heniekstar/DenshaDeGo_controller/pics/MAIN_BOARD_N64.JPG

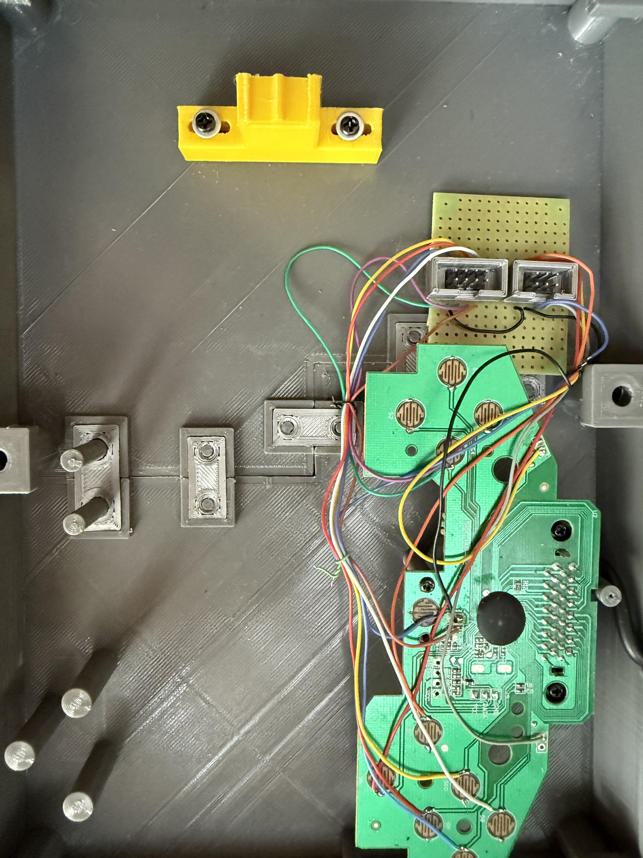
pics/MAIN_BOARD_N64.JPG
