heniekstar/DenshaDeGo_controller/pics/POGO_2.JPG

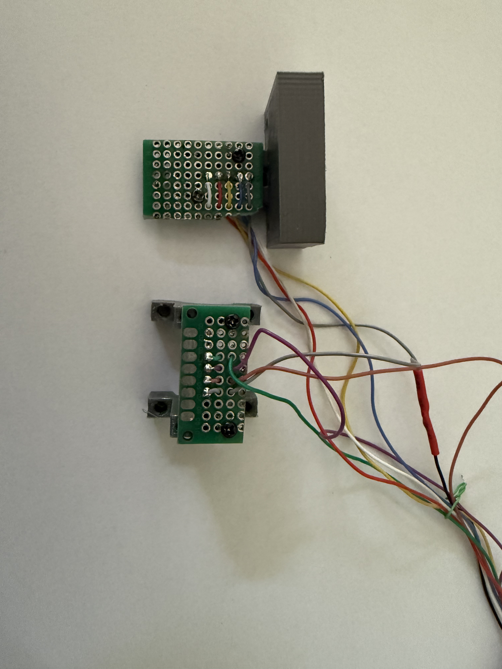
pics/POGO_2.JPG
