heniekstar/DenshaDeGo_controller/pics/POGO_POWER_WHEELS_2.JPG

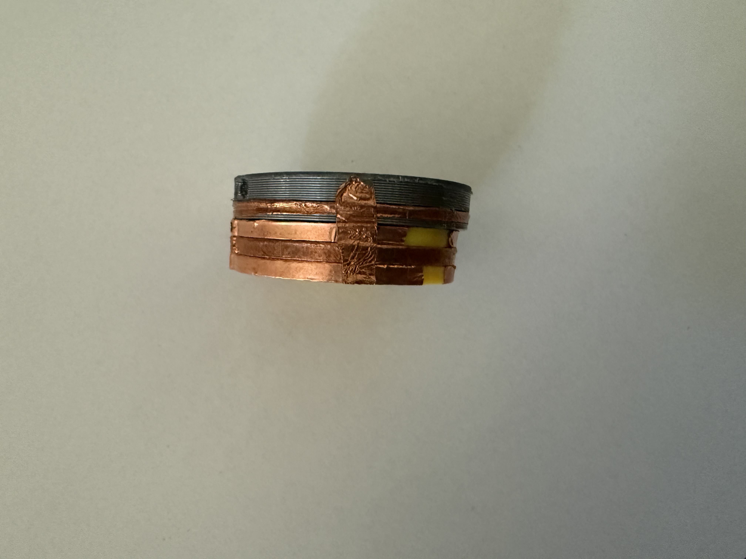
pics/POGO_POWER_WHEELS_2.JPG
