heniekstar/DenshaDeGo_controller/Limit_switch/DDG_BRAKE_WHEEL_3.stl

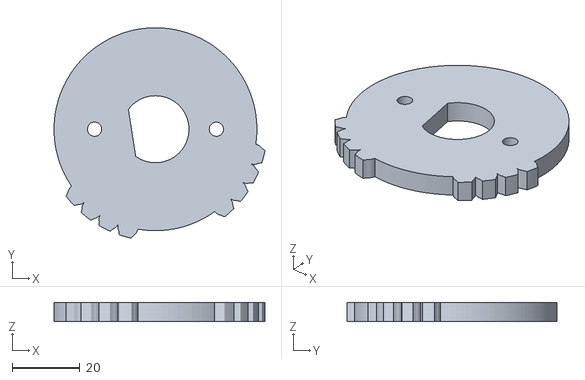
[picture p24: CAD file, 2026-08-02]
Limit_switch/DDG_BRAKE_WHEEL_3.stl
62.4 x 62.2 x 5.70
