heniekstar/DenshaDeGo_controller/Pogo/DDG_POGO_BREAK_WHEEL_2.stl

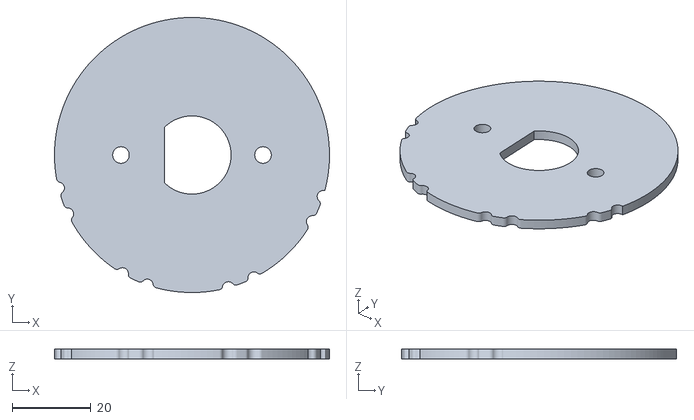
[picture p25: CAD file, 2026-08-02]
Pogo/DDG_POGO_BREAK_WHEEL_2.stl
69.7 x 69.7 x 2.50
