heniekstar/DenshaDeGo_controller/Limit_switch/DDG_BRAKE_WHEEL_4.stl

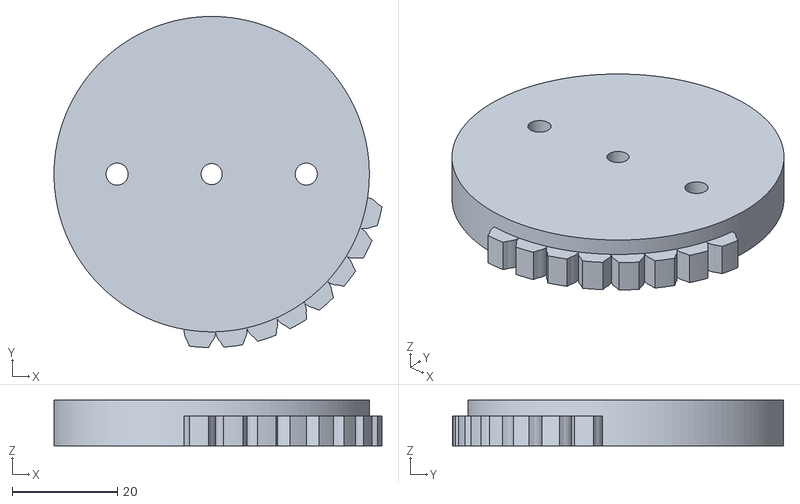
[picture p26: CAD file, 2026-08-02]
Limit_switch/DDG_BRAKE_WHEEL_4.stl
62.4 x 63.0 x 8.70
