heniekstar/DenshaDeGo_controller/Pogo/DDG_POGO_BREAK_WHEEL_0.stl

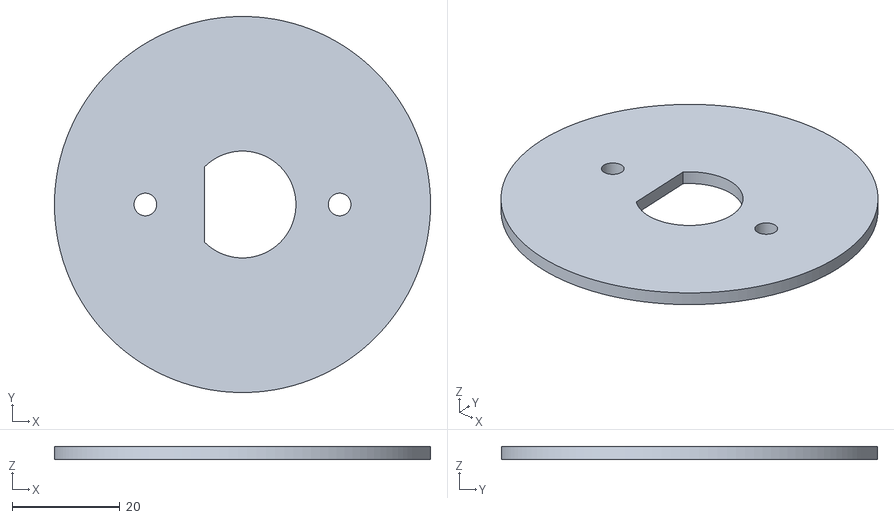
[picture p27: CAD file, 2026-08-02]
Pogo/DDG_POGO_BREAK_WHEEL_0.stl
69.7 x 69.7 x 2.50
