heniekstar/DenshaDeGo_controller/Pogo/DDG_POGO_POWER_WHEEL_MAG.stl

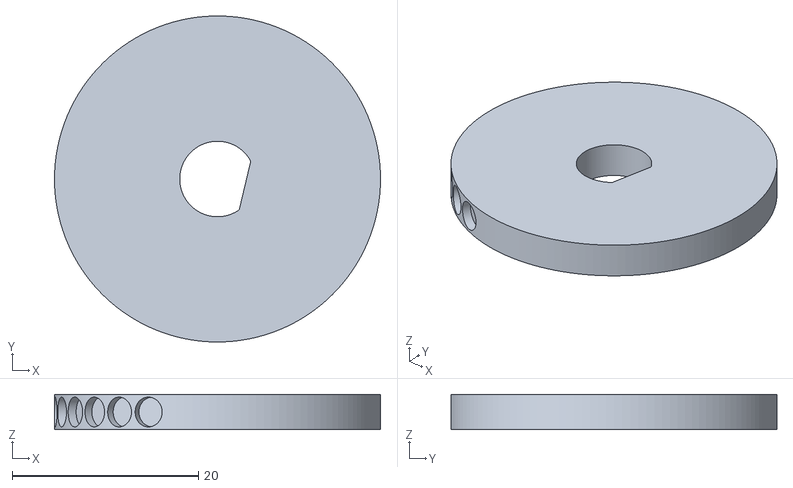
[picture p28: CAD file, 2026-08-02]
Pogo/DDG_POGO_POWER_WHEEL_MAG.stl
35.0 x 35.0 x 3.80
