heniekstar/DenshaDeGo_controller/Pogo/DDG_POGO_BREAK_WHEEL_SUPPORT.stl

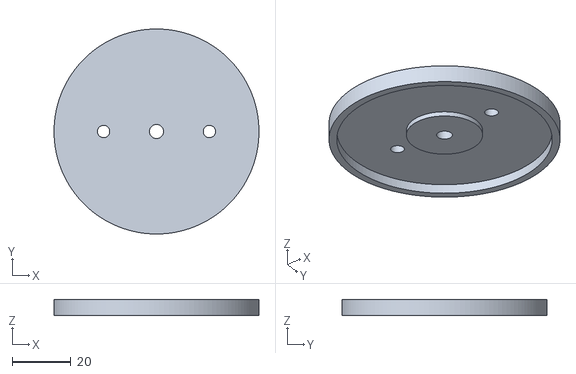
[picture p29: CAD file, 2026-08-02]
Pogo/DDG_POGO_BREAK_WHEEL_SUPPORT.stl
69.7 x 69.7 x 5.50
