heniekstar/DenshaDeGo_controller/Pogo/DDG_POWER_HANDLE_END_CAP.stl

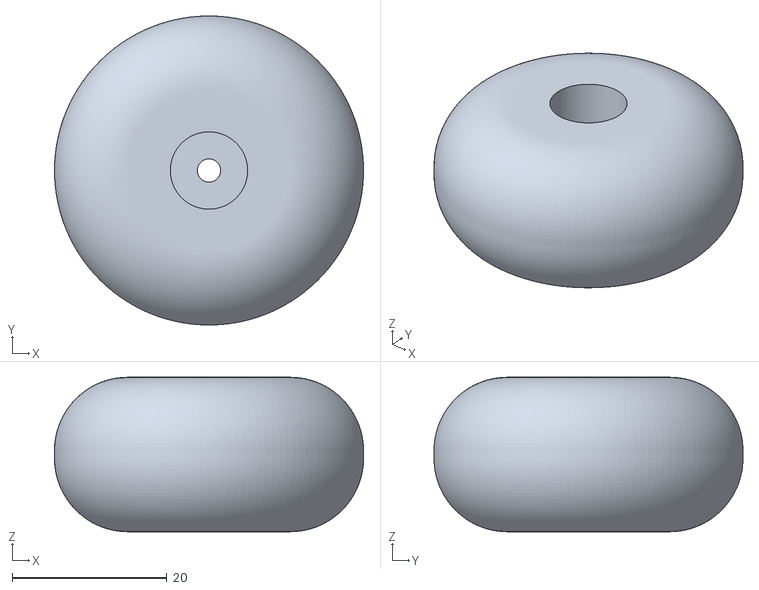
[picture p30: CAD file, 2026-08-02]
Pogo/DDG_POWER_HANDLE_END_CAP.stl
40.0 x 40.0 x 20.0
