heniekstar/DenshaDeGo_controller/Pogo/DDG_TOP&BOT_LINK.stl

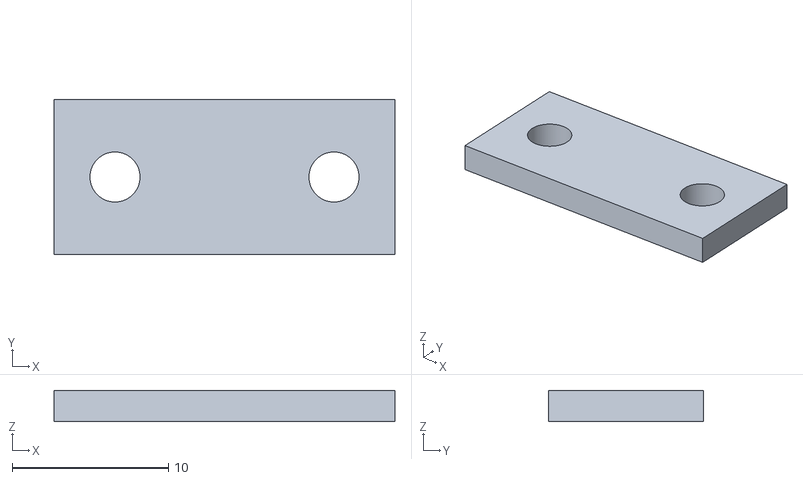
[picture p31: CAD file, 2026-08-02]
Pogo/DDG_TOP&BOT_LINK.stl
21.8 x 9.90 x 2.00
