heniekstar/DenshaDeGo_controller/Pogo/DDG_BREAK_HANDLE_BARREL.stl

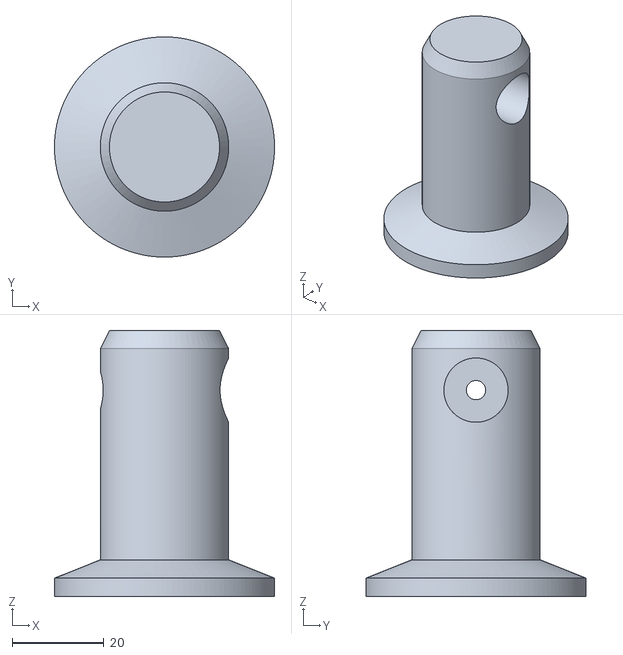
[picture p32: CAD file, 2026-08-02]
Pogo/DDG_BREAK_HANDLE_BARREL.stl
48.0 x 48.0 x 58.0
