heniekstar/DenshaDeGo_controller/Pogo/DDG_TOP_C_BUTTON.stl

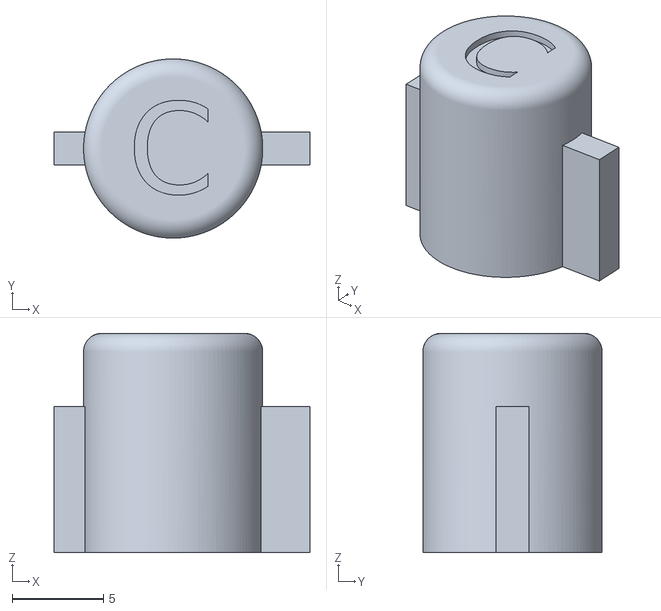
[picture p33: CAD file, 2026-08-02]
Pogo/DDG_TOP_C_BUTTON.stl
14.0 x 9.80 x 12.0
