heniekstar/DenshaDeGo_controller/Pogo/DDG_TOP_POWER_LOWER_SUPPORT.stl

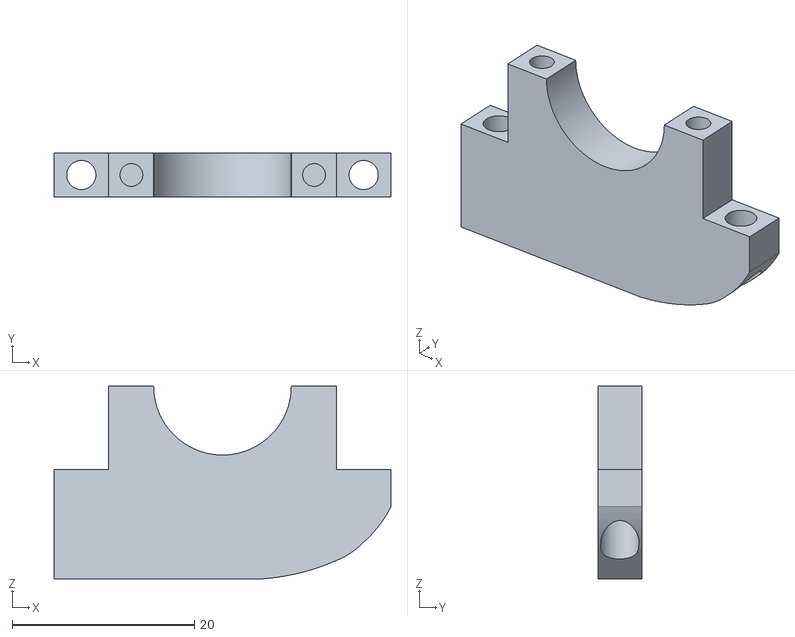
[picture p34: CAD file, 2026-08-02]
Pogo/DDG_TOP_POWER_LOWER_SUPPORT.stl
37.0 x 4.80 x 21.1
