heniekstar/DenshaDeGo_controller/Pogo/DDG_BREAK_SWITCH_HAPTIC.stl

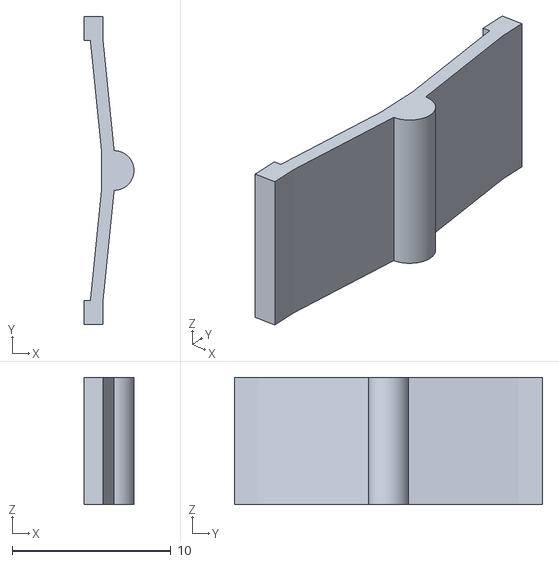
[picture p35: CAD file, 2026-08-02]
Pogo/DDG_BREAK_SWITCH_HAPTIC.stl
3.15 x 19.4 x 8.00
