heniekstar/DenshaDeGo_controller/Pogo/DDG_TOP_HOUSING-Slice.0.stl

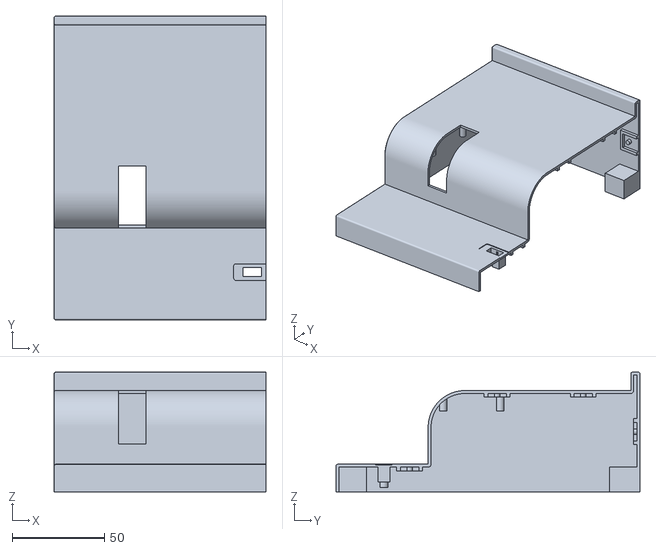
[picture p36: CAD file, 2026-08-02]
Pogo/DDG_TOP_HOUSING-Slice.0.stl
115.0 x 165.0 x 65.0
