heniekstar/DenshaDeGo_controller/Pogo/DDG_BREAK_GUIDE.stl

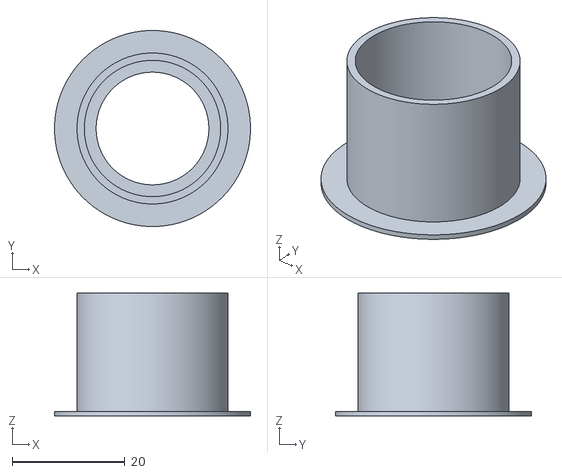
[picture p37: CAD file, 2026-08-02]
Pogo/DDG_BREAK_GUIDE.stl
34.8 x 34.8 x 21.8
