heniekstar/DenshaDeGo_controller/Pogo/DDG_TOP_START_BUTTON.stl

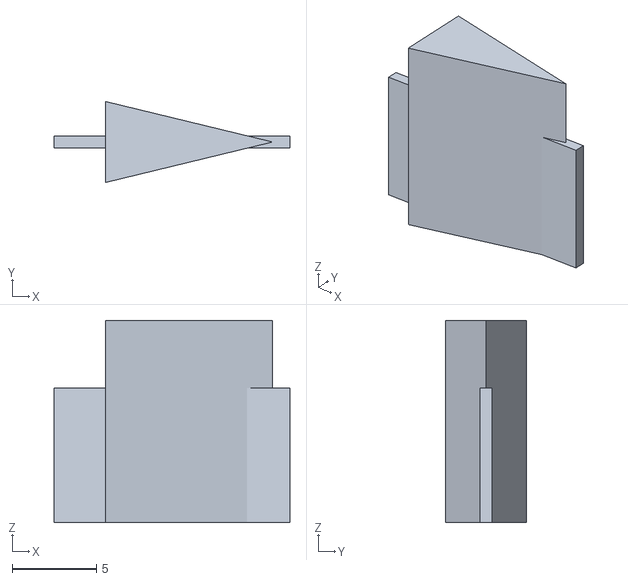
[picture p38: CAD file, 2026-08-02]
Pogo/DDG_TOP_START_BUTTON.stl
14.0 x 4.80 x 12.0
