heniekstar/DenshaDeGo_controller/Pogo/DDG_POWER_SHAFT.stl

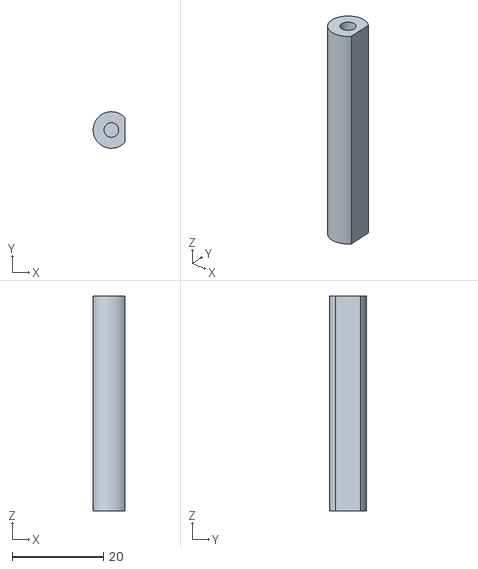
[picture p39: CAD file, 2026-08-02]
Pogo/DDG_POWER_SHAFT.stl
6.94 x 8.00 x 47.0
