heniekstar/DenshaDeGo_controller/Pogo/DDG_BOTTON_SHELL-Slice.1.stl

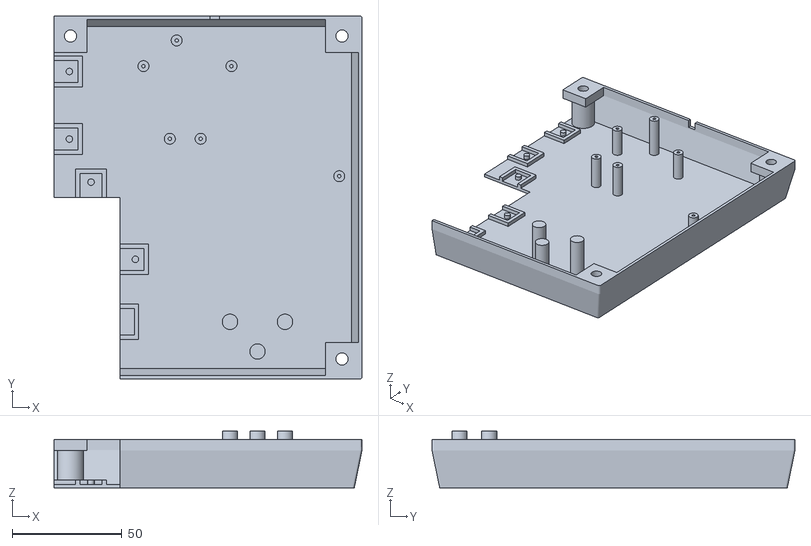
[picture p40: CAD file, 2026-08-02]
Pogo/DDG_BOTTON_SHELL-Slice.1.stl
140.0 x 165.0 x 25.8
