heniekstar/DenshaDeGo_controller/Pogo/DDG_POWER_HANDLE_WHEEL.stl

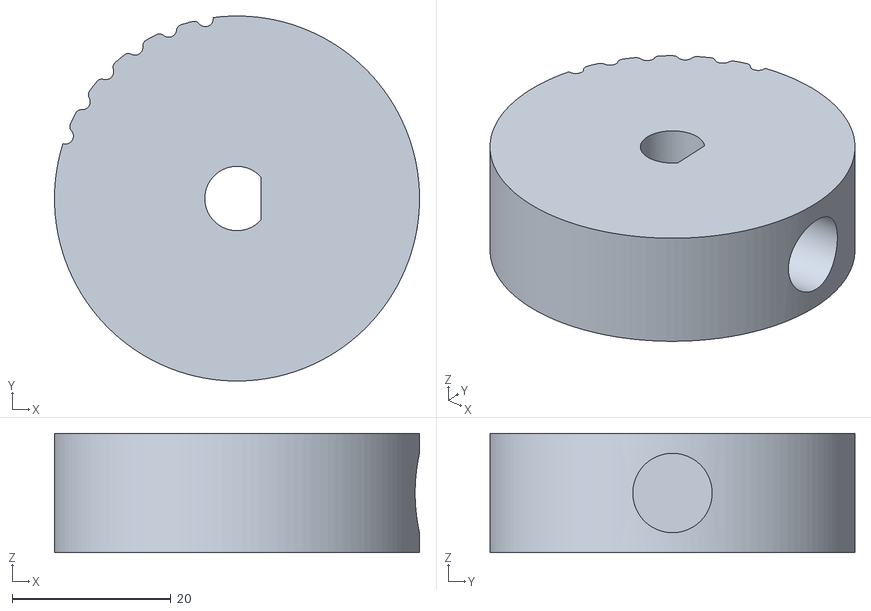
[picture p41: CAD file, 2026-08-02]
Pogo/DDG_POWER_HANDLE_WHEEL.stl
46.0 x 46.0 x 15.0
