heniekstar/DenshaDeGo_controller/Pogo/DDG_BOTTON_SHELL.stl

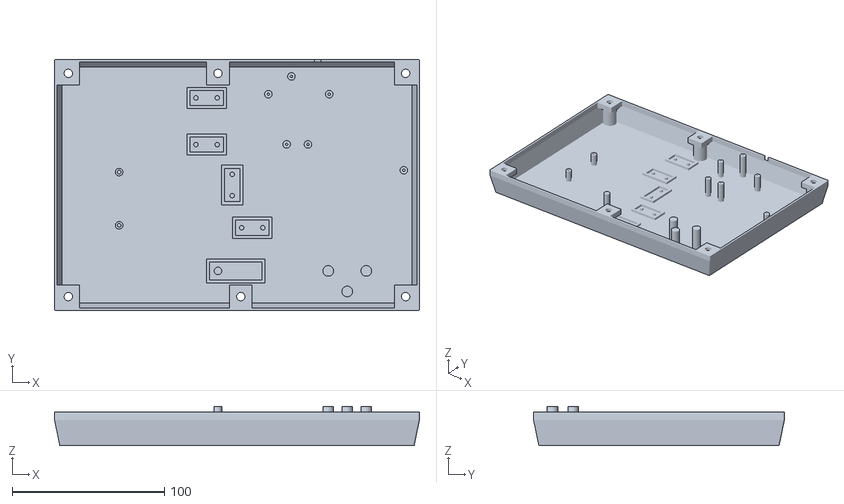
[picture p42: CAD file, 2026-08-02]
Pogo/DDG_BOTTON_SHELL.stl
240.0 x 165.0 x 25.8
