heniekstar/DenshaDeGo_controller/Pogo/DDG_POWER_RING.stl

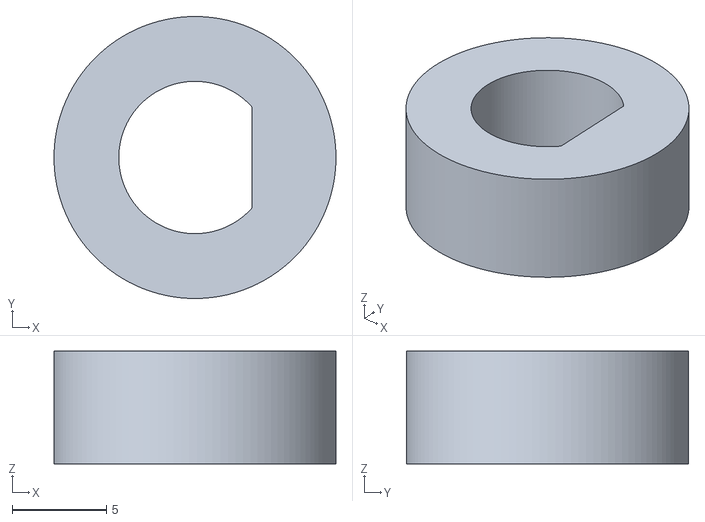
[picture p43: CAD file, 2026-08-02]
Pogo/DDG_POWER_RING.stl
15.0 x 15.0 x 6.00
