heniekstar/DenshaDeGo_controller/Pogo/DDG_BOTTON_SHELL-Slice.0.stl

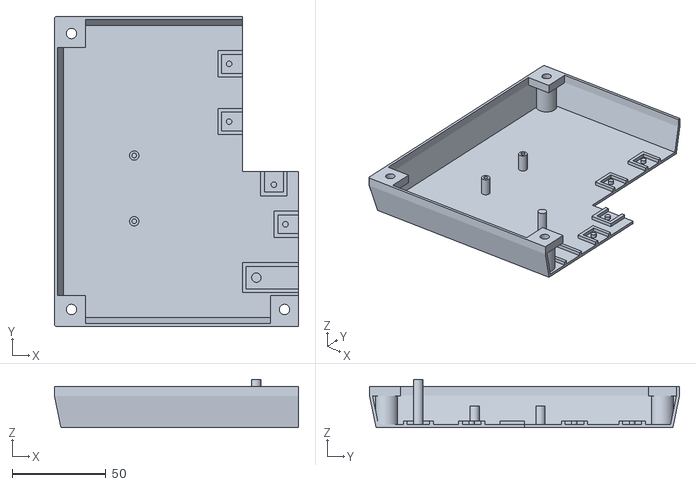
[picture p44: CAD file, 2026-08-02]
Pogo/DDG_BOTTON_SHELL-Slice.0.stl
130.0 x 165.0 x 25.8
