heniekstar/DenshaDeGo_controller/Pogo/DDG_POWER_HANDLE_ANGLE.stl

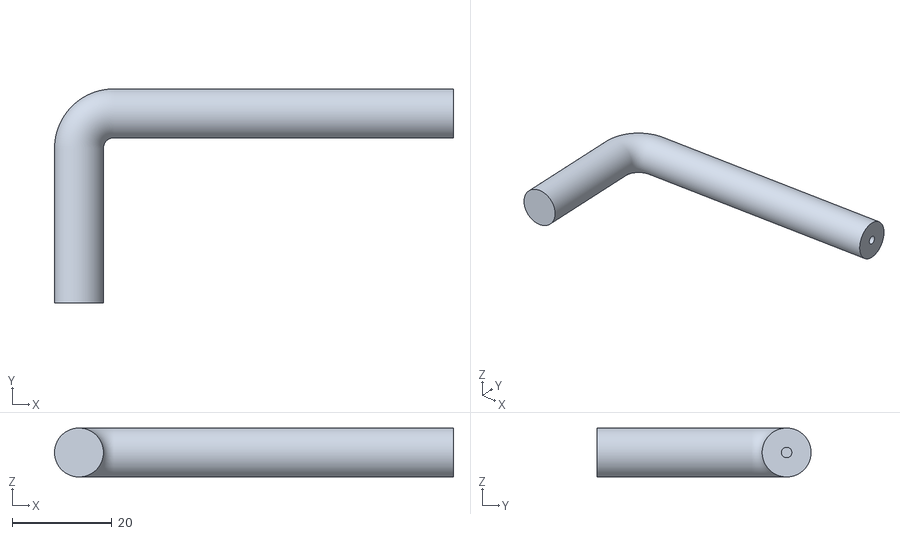
[picture p45: CAD file, 2026-08-02]
Pogo/DDG_POWER_HANDLE_ANGLE.stl
79.9 x 42.9 x 9.80
