heniekstar/DenshaDeGo_controller/Pogo/DDG_POWER_END_CAP.stl

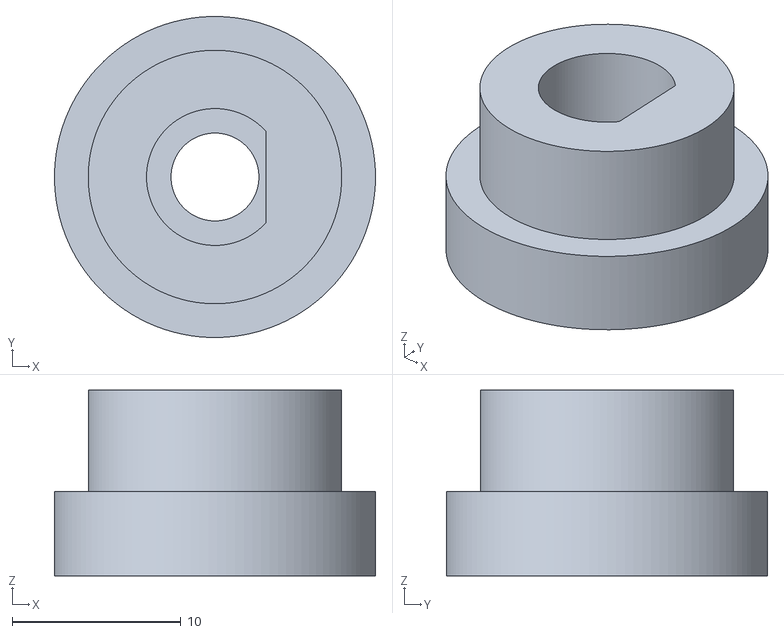
[picture p46: CAD file, 2026-08-02]
Pogo/DDG_POWER_END_CAP.stl
19.0 x 19.0 x 11.0
