heniekstar/DenshaDeGo_controller/Pogo/DDG_POWER_HAPTIC_1.stl

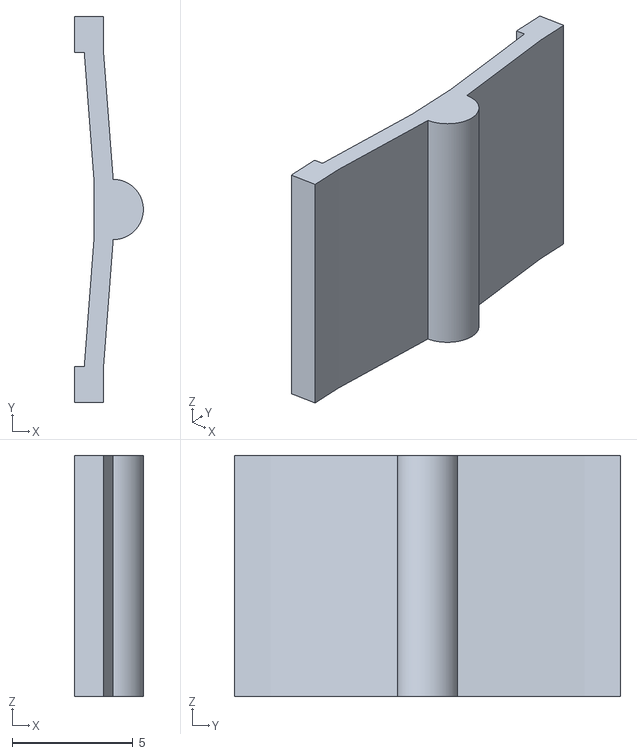
[picture p47: CAD file, 2026-08-02]
Pogo/DDG_POWER_HAPTIC_1.stl
2.85 x 16.0 x 10.0
