heniekstar/DenshaDeGo_controller/Pogo/DDG_BREAK_HANDLE_BARREL_GUIDE.stl

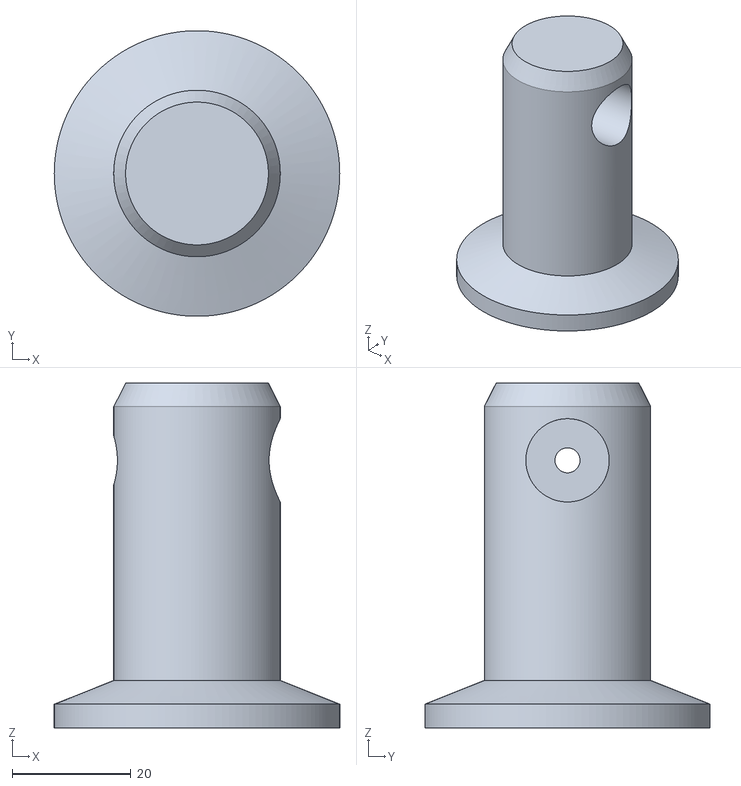
[picture p48: CAD file, 2026-08-02]
Pogo/DDG_BREAK_HANDLE_BARREL_GUIDE.stl
48.0 x 48.0 x 58.0
