heniekstar/DenshaDeGo_controller/Pogo/DDG_BOTTOM_START_SUPPORT.stl

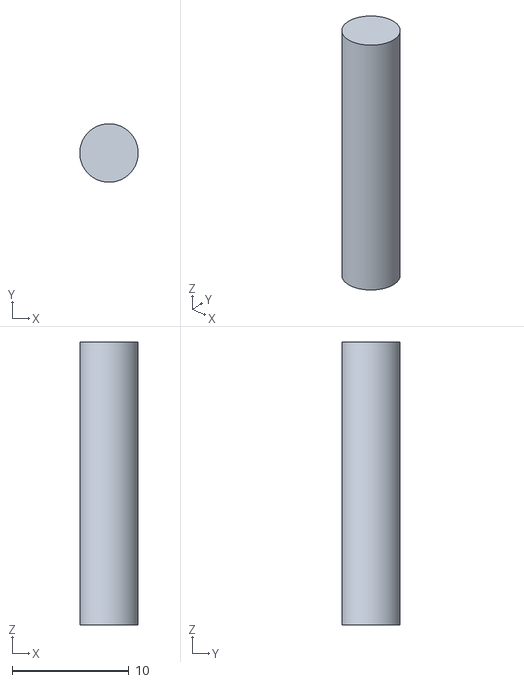
[picture p49: CAD file, 2026-08-02]
Pogo/DDG_BOTTOM_START_SUPPORT.stl
5.00 x 5.00 x 24.2
