heniekstar/DenshaDeGo_controller/Pogo/DDG_POWER_HAPTIC_HOLDER.stl

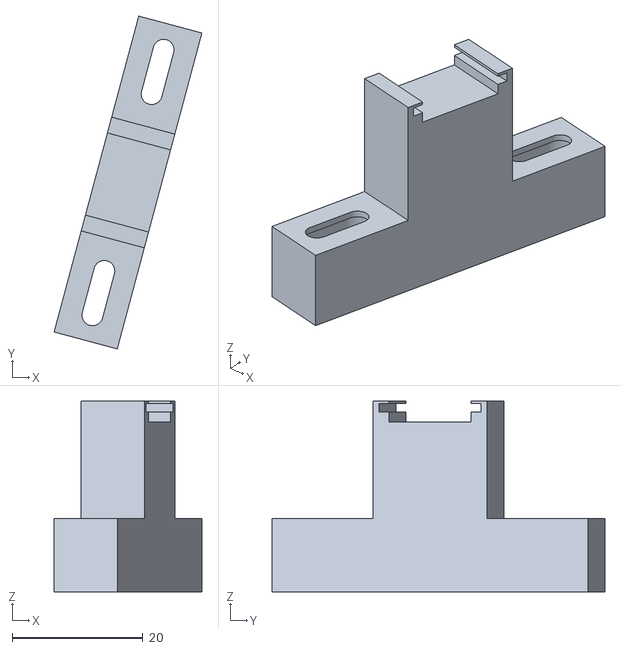
[picture p50: CAD file, 2026-08-02]
Pogo/DDG_POWER_HAPTIC_HOLDER.stl
22.6 x 50.9 x 29.2
