heniekstar/DenshaDeGo_controller/Pogo/DDG_BRAKE_WHEEL_HAPTIC.stl

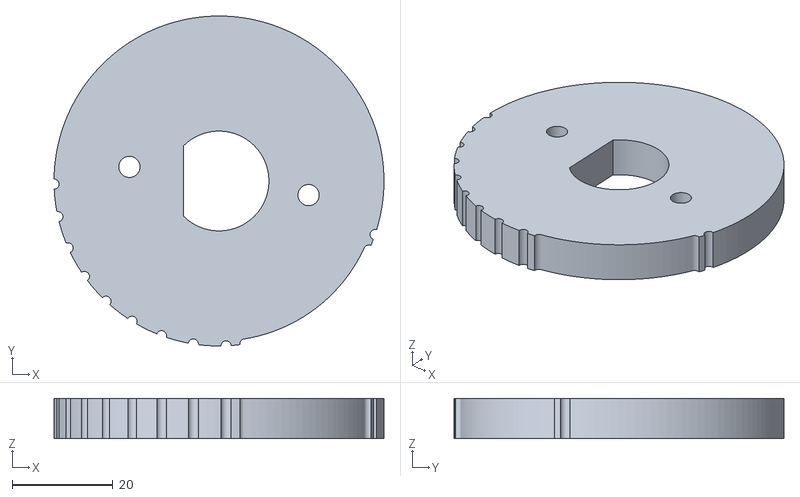
[picture p51: CAD file, 2026-08-02]
Pogo/DDG_BRAKE_WHEEL_HAPTIC.stl
65.5 x 65.5 x 8.00
