heniekstar/DenshaDeGo_controller/Pogo/DDG_TOP_SELECT_BUTTON.stl

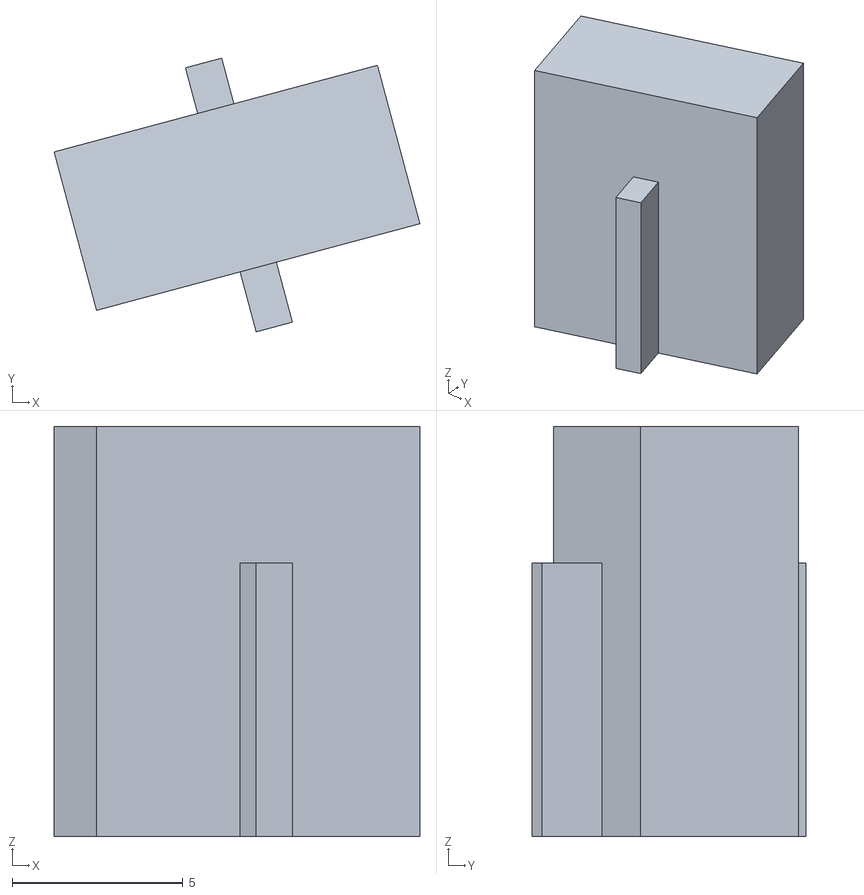
[picture p52: CAD file, 2026-08-02]
Pogo/DDG_TOP_SELECT_BUTTON.stl
10.7 x 8.01 x 12.0
