heniekstar/DenshaDeGo_controller/Pogo/DDG_TOP_HOUSING.stl

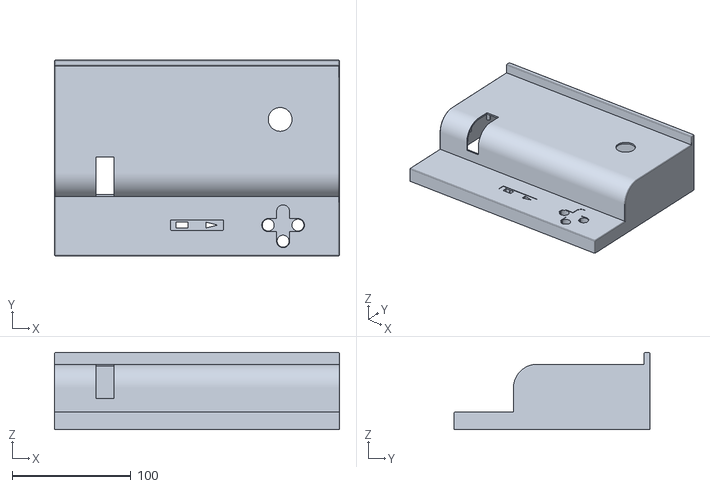
[picture p53: CAD file, 2026-08-02]
Pogo/DDG_TOP_HOUSING.stl
240.0 x 165.0 x 65.0
