heniekstar/DenshaDeGo_controller/Pogo/DDG_BREAK_SHAFT.stl

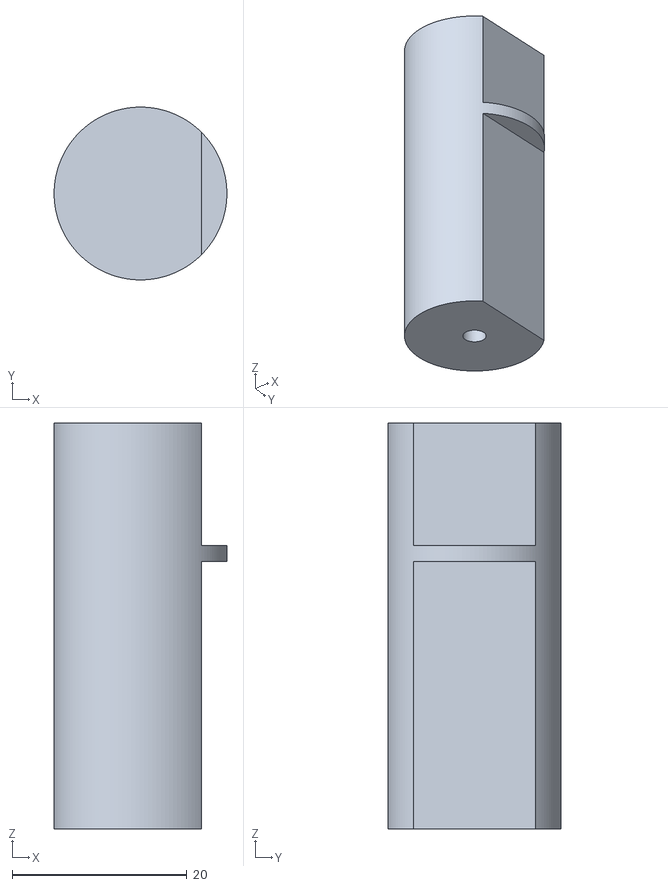
[picture p54: CAD file, 2026-08-02]
Pogo/DDG_BREAK_SHAFT.stl
19.7 x 19.7 x 46.4
