heniekstar/DenshaDeGo_controller/Pogo/DDG_TOP_HOUSING-Slice.1.stl

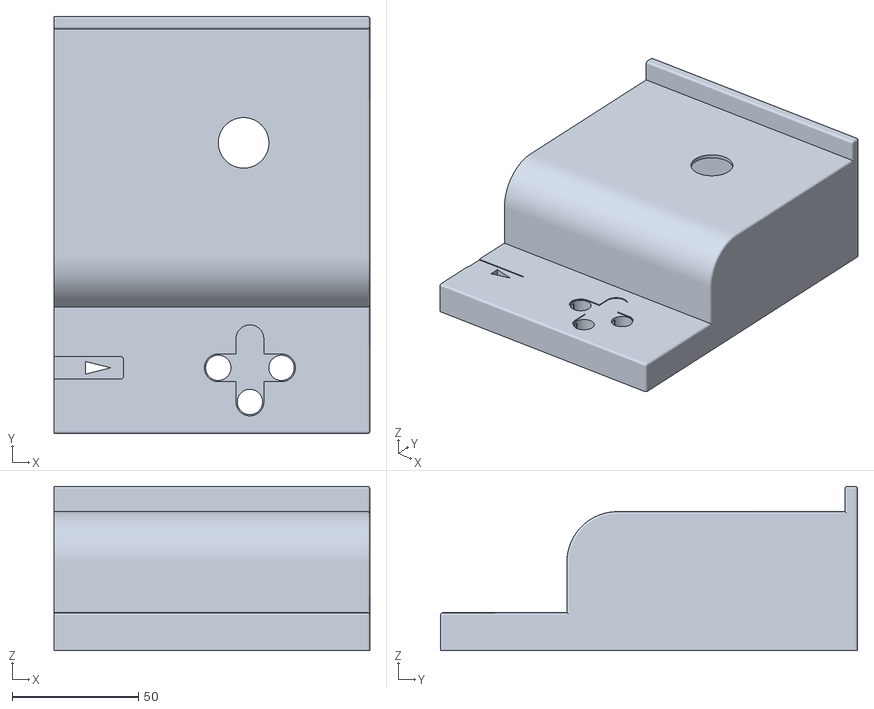
[picture p55: CAD file, 2026-08-02]
Pogo/DDG_TOP_HOUSING-Slice.1.stl
125.0 x 165.0 x 65.0
