heniekstar/DenshaDeGo_controller/Pogo/DDG_BOT_STR_SEL_LINK.stl

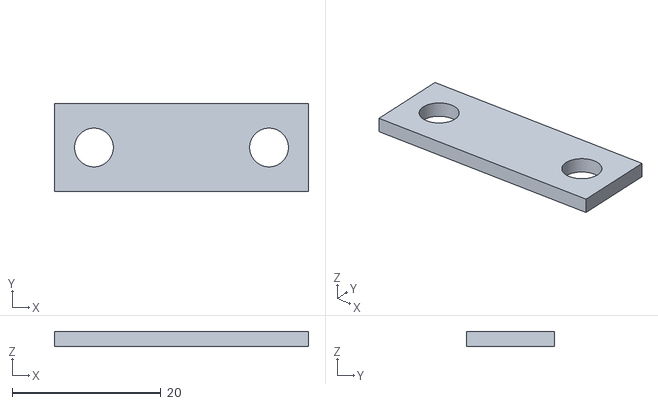
[picture p56: CAD file, 2026-08-02]
Pogo/DDG_BOT_STR_SEL_LINK.stl
34.1 x 11.8 x 2.00
